HangX-Ma/MiniScpoe-STC8A/User/src/uart.c

/**
 * @file uart.c
 * @author MContour (m-contour@qq.com)
 * @brief UART functions realization
 * @version 0.1
 * @date 2022-05-15
 * 
 * @copyright Apache 2.0 LICENSE
 * 
 *****************************************************************************
 * Copyright (c) 2022 MContour m-contour@qq.com
 *
 * Licensed under the Apache License, Version 2.0 (the "License");
 * you may not use this file except in compliance with the License.
 * You may obtain a copy of the License at
 * 
 *     http://www.apache.org/licenses/LICENSE-2.0
 * 
 * Unless required by applicable law or agreed to in writing, software
 * distributed under the License is distributed on an "AS IS" BASIS,
 * WITHOUT WARRANTIES OR CONDITIONS OF ANY KIND, either express or implied.
 * See the License for the specific language governing permissions and
 * limitations under the License.
 *****************************************************************************
 */

#include "uart.h"
#include "fifo.h"
#include "global_var.h"
#include "STRING.H"


bit isUART1_Tx_IDLE;
bit isUART1_Rx_IDLE;
FIFO_struct xdata UART1_Rx;
uint8_t UARTx_Rx_NmsTimeout;
bit isUARTx_Rx_Timeout;

#if (UARTx_MODE == UARTx_DMA_MODE)
DMABuf_TypeDef CurrFreeBuf;
uint8_t xdata UART1_Tx_DMABuffer[UART1_DMA_BUF_LENGTH];
uint8_t xdata UART1_Rx_DMABuffer[2][UART1_DMA_BUF_LENGTH];
#endif

void TM3_Init(void) {
    T4T3M |= T4T3M_T3R;     // Disable TM3 until it is enabled in UARTx interrupt
    T4T3M &= ~T4T3M_T3_CT;  // Select TM3 as timer
    T4T3M &= ~T4T3M_T3CLKO; // Disable clock ticks output
    T4T3M |= T4T3M_T3x12;   // 1T
    /* 1ms Timer setting */
    #if (LIB_MCU_MODULE == STC8Hx)
        TM3PS = 0x00;
        T3H = (65536 - LIB_CLK_FREQ/(TM3PS+1)/1000) / 256 ;
        T3L = (65536 - LIB_CLK_FREQ/(TM3PS+1)/1000) % 256 ;
    #elif (LIB_MCU_MODULE == STC8Ax) 
        T3H = (65536 - LIB_CLK_FREQ/1000) / 256 ;
        T3L = (65536 - LIB_CLK_FREQ/1000) % 256 ;
    #endif
    IE2  |= IE2_ET3; // Enable TM3 interrupt
}


void UART1_Init(void) {
    /* TM2 16 bits automatically reloading mode */
    AUXR  |= AUXR_S1ST2;    // Select TM2 as the bund rate generator
    AUXR  &= ~AUXR_T2R;     // Stop TM2
    AUXR  &= ~AUXR_T2CT;    // Select TM2 as Timer
    AUXR  |= AUXR_T2x12;    // 1T Mode, No frequency division
    T2L    = 0x8F;          // Reload Value Low Byte
    T2H    = 0xFD;          // Reload Value High Byte
    IE2   &= ~IE2_ET2;      // Forbidden TM2 interrupt
    AUXR  |= AUXR_T2R;      // Start TM2
    S1CON  = 0x50;          // Mode1, variable bund rate, 8 bits data
    ES     = SETBIT;        // Enable UART1 interrupt
    S1REN  = SETBIT;        // Enable UART1 receiver
    // PS     = SETBIT;     // Interrupt Level 1
    // TM3_Init();
    P_SW1 &= (~P_SW1_S1_S); // P3.0 RxD, P3.1 TxD
    P_SW1 |= P_SW1_S1_S_GROUP1;
    isUART1_Tx_IDLE    = SETBIT;
    isUART1_Rx_IDLE    = SETBIT;
    FIFO_Init(&UART1_Rx);
    isUARTx_Rx_Timeout = CLRBIT;
    FIFO_Threshold     = FIFO_Threshold_15; // default threshold value
}

void UARTx_Send(uint8_t chr) {
    S1BUF = chr;
    isUART1_Tx_IDLE = CLRBIT;
    while (!isUART1_Tx_IDLE) {
        ;
    }
}

void UARTx_Send_String(uint8_t *str) {
    while (*str) {
        UARTx_Send(*str++);
    }
}

ErrorStatus UARTx_Receive(uint8_t *strPtr) {
    uint8_t tmpData;

    if (isUART1_Rx_IDLE) {
        return ERROR;
    } // Rx FIFO buffer is empty. No data is retrieved.

    /* Prepare receiving data from FIFO buffer */
    UARTx_Rx_NmsTimeout = UARTx_RX_Nms_TIMEOUT_VAL; // Set timeout (nms) value
    isUARTx_Rx_Timeout  = CLRBIT; // clear Timeout flag
    T4T3M |= T4T3M_T3R; // Start TM3 

    while (!isUARTx_Rx_Timeout) {
        if (FIFO_empty == FIFO_Out(&UART1_Rx, &tmpData)) {
            continue;
        } // If UART1_Rx has no data, continue listening to FIFO
        else {
            /* If UART1_Rx buffer has data, we update the receiving timeout value */
            UARTx_Rx_NmsTimeout = UARTx_RX_Nms_TIMEOUT_VAL; 
            *strPtr++ = tmpData;
        } // FIFO buffer has data
    }

    return SUCCESS;
}

/**
 * @brief MCU UART1 interrupt service 
 */
void UART1_ISR_Handler(void) interrupt(UART1_VECTOR) using(1) {
    if(S1TI) {
        S1TI            = CLRBIT; // prepare for next interrupt
        isUART1_Tx_IDLE = SETBIT; // data has been sent, Rx buffer become IDLE again
    }

    if (S1RI) {
        if (FIFO_succ == FIFO_In(&UART1_Rx, S1BUF)) {
            if (Get_FIFO_UsedSpace(&UART1_Rx) == (uint8_t)FIFO_Threshold) {
                isUART1_Rx_IDLE = CLRBIT; // Rx buffer has data now
            } // Indicate serial port has received enough data, otherwise continuing receiving data.
        } // Store data. if returned value is FIFO_full, indicating additional data has lost
        else {
            isUART1_Rx_IDLE = CLRBIT; // Rx buffer has data now
        } // FIFO buffer is FULL
        S1RI = CLRBIT;          // prepare for next interrupt
    } // This design guarantees the instantaneity of UART receiving process and protect the data by using buffer.
}


void TM3_ISR_Handler(void) interrupt(TM3_VECTOR) using(3) {
    if (UARTx_Rx_NmsTimeout > 0) {
        UARTx_Rx_NmsTimeout--;
    }
    else if (UARTx_Rx_NmsTimeout == 0) {
        T4T3M &= ~T4T3M_T3R; // stop TM3
        isUARTx_Rx_Timeout = SETBIT;
    }
}

#if (UARTx_MODE == UARTx_DMA_MODE)
/**
 * @brief UART1 BMM
 * @note Because the interrupt vector is greater than 31, 
 * you can not compile directly in Keil and must borrow 
 * the interrupt entry address No.13.
 */
void UART1_BMM_Interrupt(void) interrupt(13) {
    if (UR1T_BMM->STA & BMM_UR1T_STA_UR1TIF) {
        UR1T_BMM->STA &= ~BMM_UR1T_STA_UR1TIF; // Clear DMA interrupt flag
        UR1T_BMM->CR   = 0x00;
        memset(UART1_Tx_DMABuffer, (uint8_t)0, sizeof(UART1_Tx_DMABuffer)/sizeof(uint8_t));
    } // Sending complete

    if (UR1T_BMM->STA & BMM_UR1T_STA_TXOVW) {
        UR1T_BMM->STA &= ~BMM_UR1T_STA_TXOVW;
    } // Data overwrite. Sending process continues.

    if (UR1R_BMM->STA & BMM_UR1R_STA_UR1RIF) {
        UR1R_BMM->STA &= ~BMM_UR1R_STA_UR1RIF;

        P_SW2 |= P_SW2_EAXFR;
        if (CurrFreeBuf == Sel_Rx_DMABuf1) {
            memset(UART1_Rx_DMABuffer[CurrFreeBuf], (uint8_t)0, sizeof(UART1_Rx_DMABuffer[CurrFreeBuf])/sizeof(uint8_t));
            UR1R_BMM->TXA = (uint16_t)UART1_Rx_DMABuffer[Sel_Rx_DMABuf1];
            CurrFreeBuf = Sel_Rx_DMABuf2;
        }
        else if  (CurrFreeBuf == Sel_Rx_DMABuf2) {
            memset(UART1_Rx_DMABuffer[CurrFreeBuf], (uint8_t)0, sizeof(UART1_Rx_DMABuffer[CurrFreeBuf])/sizeof(uint8_t));
            UR1R_BMM->TXA = (uint16_t)UART1_Rx_DMABuffer[Sel_Rx_DMABuf2];
            CurrFreeBuf = Sel_Rx_DMABuf1;
        }
        P_SW2 &= ~P_SW2_EAXFR;
    } // Receiving complete

    if (UR1R_BMM->STA & BMM_UR1R_STA_RXLOSS) {
        UR1R_BMM->STA &= ~BMM_UR1R_STA_RXLOSS;
    } // Data discarded. Receiving process continues.
}

void UART1_BMM_Config(void) {
    P_SW2 |= P_SW2_EAXFR;
    UR1T_BMM->CFG |= BMM_UR1T_CFG_UR1TIE;                           // Enable BMM interrupt
    UR1T_BMM->CR  &= ~(BMM_UR1T_CR_ENUR1T | BMM_UR1T_CR_TRIG);      // Disable UR1T_BMM function and UR1T_BMM 
    UR1T_BMM->STA  = 0x00;                                          // Clear STA previous value
    UR1T_BMM->AMT  = (uint8_t)(UART1_DMA_BUF_LENGTH - 1);           // Set total transferred bytes: n+1
    UR1T_BMM->TXA  = (uint16_t)UART1_Tx_DMABuffer;                  // Get buffer Address

    UR1R_BMM->CFG |= BMM_UR1R_CFG_UR1RIE;                           // Enable BMM interrupt
    UR1R_BMM->CR  |= (BMM_UR1R_CR_ENUR1R | BMM_UR1R_CR_TRIG | BMM_UR1R_CR_CLRFIFO); // Enable UR1R_BMM function, UR1R_BMM and CLRFIFO 
    UR1R_BMM->STA  = 0x00;                                          // Clear STA previous value
    UR1R_BMM->AMT  = (uint8_t)(UART1_DMA_BUF_LENGTH - 1);           // Set total transferred bytes: n+1
    UR1R_BMM->TXA  = (uint16_t)UART1_Rx_DMABuffer[Sel_Rx_DMABuf1];  // Get buffer Address
    /* Select Rx DMA Buffer1 first, so current Free Buffer is Buffer2 */
    CurrFreeBuf    = Sel_Rx_DMABuf2;
    P_SW2 &= ~P_SW2_EAXFR;
}

void UARTx_DMA_Send_String(const uint8_t *str) {
    uint8_t UART1_DMA_Cnt = 0;
    /* disable DMA interrupt while preparing data */
    UR1T_BMM->CFG &= BMM_UR1T_CFG_UR1TIE;
    UR1R_BMM->CFG &= BMM_UR1R_CFG_UR1RIE;

    /* data preparing */
    while (*str != '\0') {
        UART1_Tx_DMABuffer[UART1_DMA_Cnt++] = *str;
        if (UART1_DMA_Cnt >= UART1_DMA_BUF_LENGTH) {
            UART1_DMA_Cnt = 0;
        } // overflow protection
    }

    /* enable DMA interrupt */
    UR1T_BMM->CFG &= BMM_UR1T_CFG_UR1TIE;
    UR1R_BMM->CFG &= BMM_UR1R_CFG_UR1RIE;
    // start DMA
    UR1T_BMM->CR  |= BMM_UR1T_CR_ENUR1T | BMM_UR1T_CR_TRIG;
}

#endif
